SamMantell/MixLit/Firmware/Arduino/MixLitFirmware/definitions.h

// definitions for the MixLit

#define NUM_OF_SLIDERS 5
#define NUM_OF_POTENTIOMETERS 3/*2*/
#define NUM_OF_LED_STRIPS 5
#define NUM_OF_LEDS_PER_STRIP 8
#define NUM_OF_BUTTONS 5

#define SLIDER_DENOISE 5
#define POTENTIOMETER_DENOISE 5

#define STRING_PRODUCT "TEST"
